jrymk/q1pro-mods/Build Plate Guide/MakerWorld/photo_2024-04-15_19-17-41.jpg

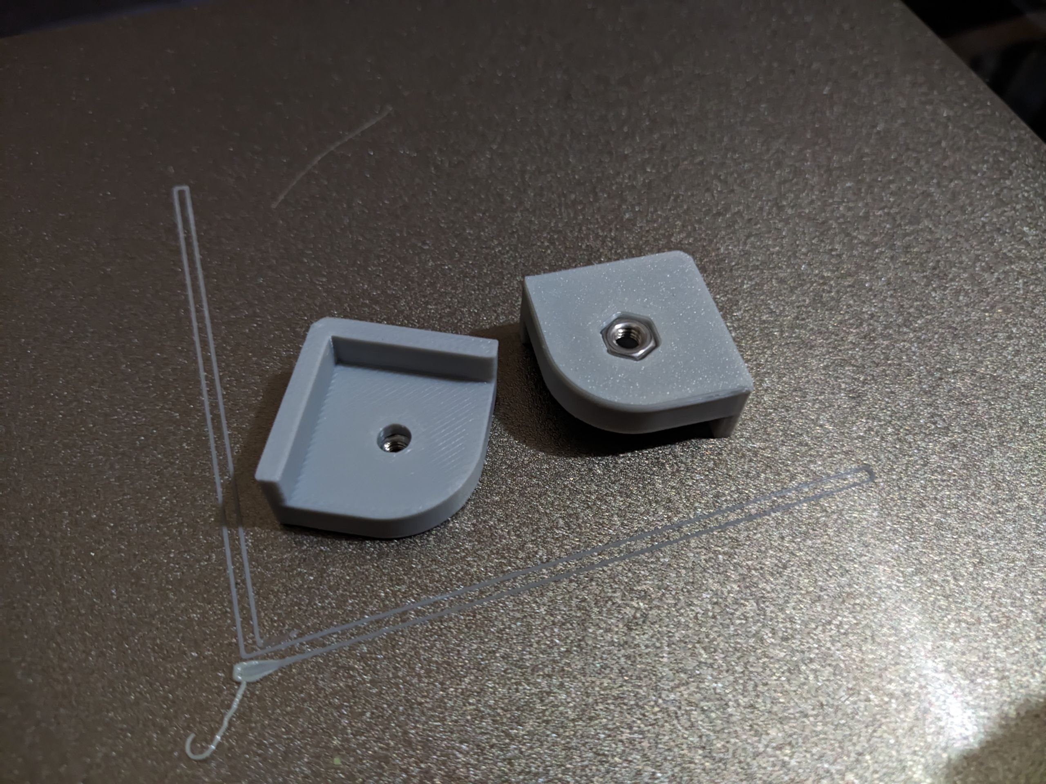
Build Plate Guide/MakerWorld/photo_2024-04-15_19-17-41.jpg
