jrymk/q1pro-mods/Build Plate Guide/MakerWorld/photo_2024-04-15_19-19-24.jpg

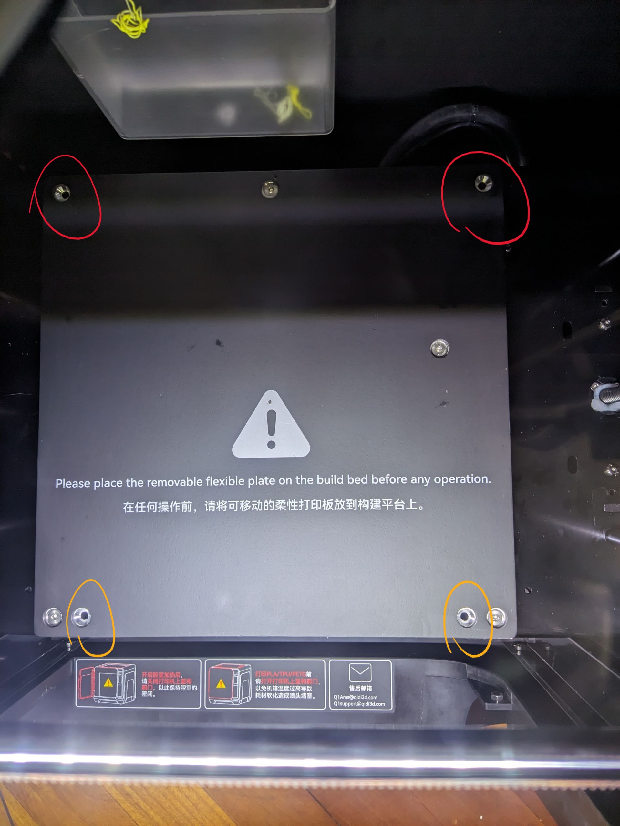
Build Plate Guide/MakerWorld/photo_2024-04-15_19-19-24.jpg
