jrymk/q1pro-mods/Ugly Spool Holder/MakerWorld/photo_1_2024-04-17_17-56-13.jpg

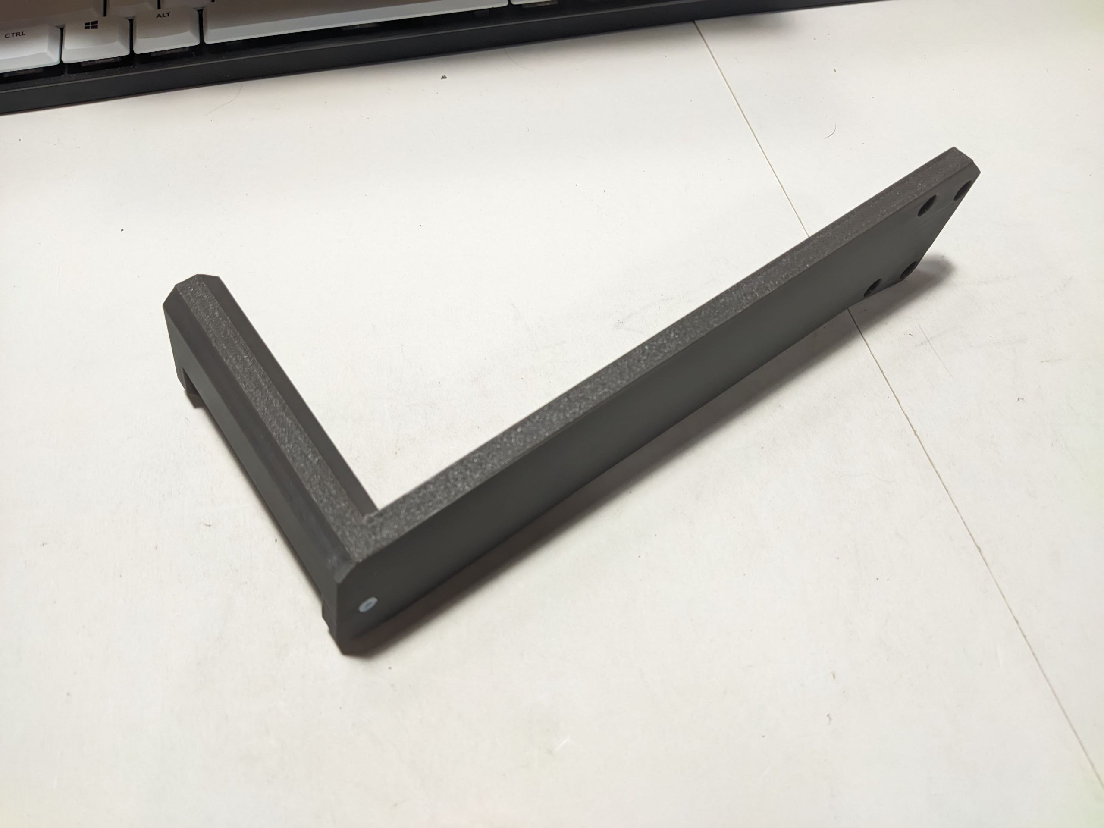
Ugly Spool Holder/MakerWorld/photo_1_2024-04-17_17-56-13.jpg
