jrymk/q1pro-mods/Ugly Spool Holder/MakerWorld/photo_2024-04-17_17-43-04.jpg

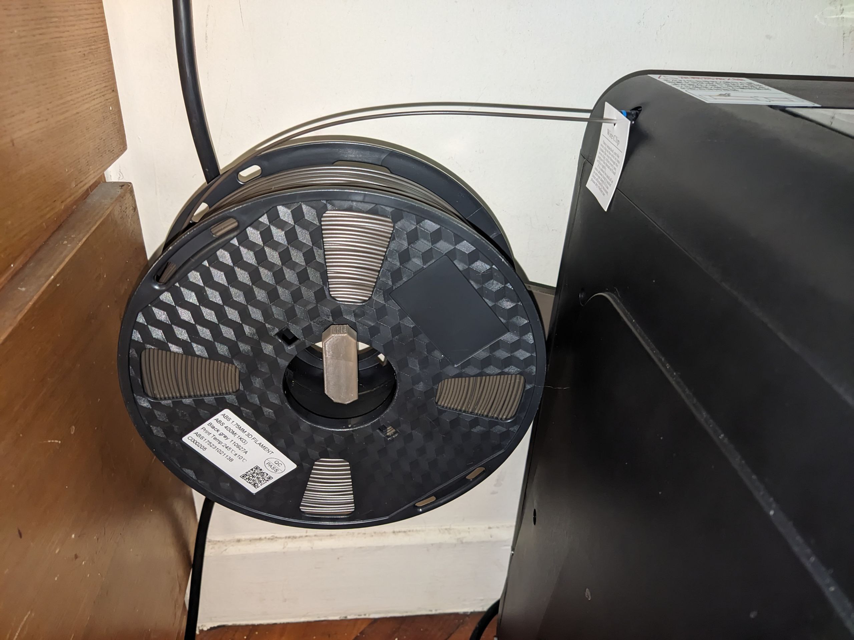
Ugly Spool Holder/MakerWorld/photo_2024-04-17_17-43-04.jpg
